diva-eng/BOKAKA/hardware/bokaka/connectors.kicad_sch

## KiCad design hardware/bokaka/connectors.kicad_sch (2026-01-29, an earlier design)

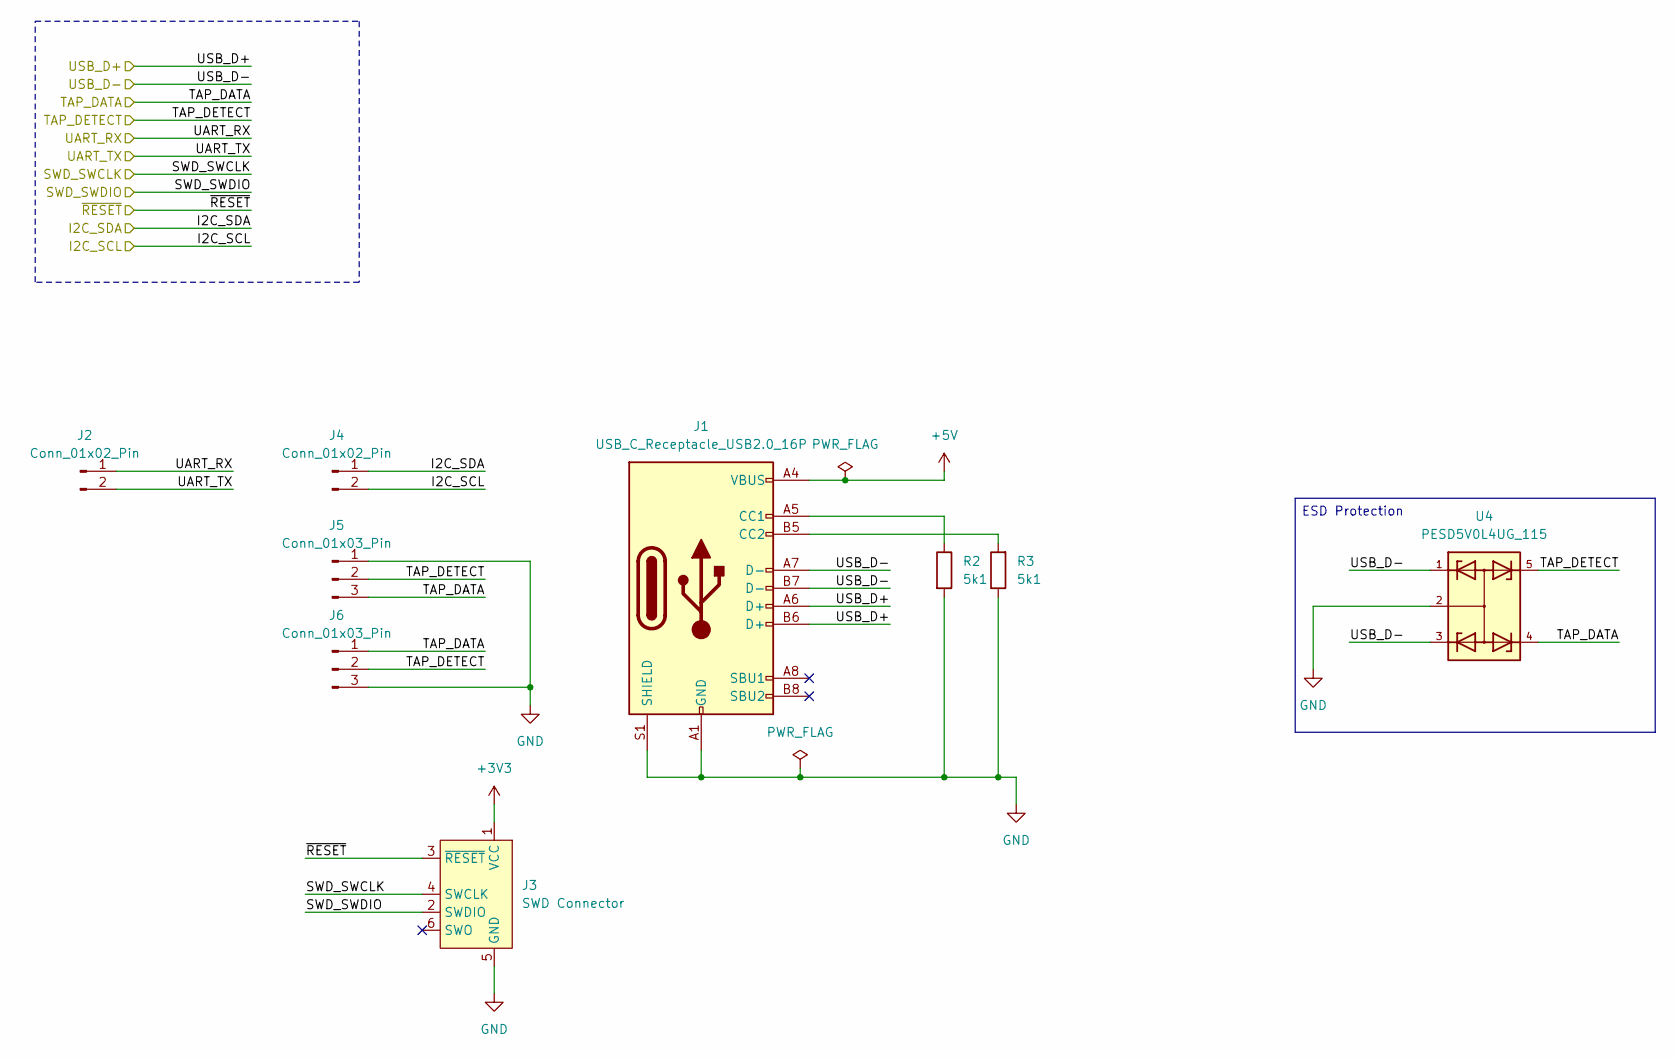
[picture p14: schematic connectors.kicad_sch]

Parts:
J1: USB_C_Receptacle_USB2.0_16P
J2, J4: Conn_01x02_Pin
J3: SWD Connector; Edge_Connect_6
J5, J6: Conn_01x03_Pin
R2, R3: 5k1; R_0402_1005Metric
U4: PESD5V0L4UG_115; SOT65P210X110-5N; PARTREV 04

Connections:
+3V3: J3.1 (VCC)
+5V: J1.A4 (VBUS), J1.A9 (VBUS), J1.B4 (VBUS), J1.B9 (VBUS)
GND: J1.A1 (GND), J1.A12 (GND), J1.B1 (GND), J1.B12 (GND), J1.S1 (SHIELD), J3.5 (GND), J5.1, J6.3, R2.2, R3.1, U4.2
I2C_SCL: J4.2
I2C_SDA: J4.1
unnamed: J1.A5 (CC1), R2.1
unnamed: J1.B5 (CC2), R3.2
SWD_SWCLK: J3.4 (SWCLK)
SWD_SWDIO: J3.2 (SWDIO)
TAP_DATA: J5.3, J6.1, U4.4
TAP_DETECT: J5.2, J6.2, U4.5
UART_RX: J2.1
UART_TX: J2.2
USB_D+: J1.A6 (D+), J1.B6 (D+)
USB_D-: J1.A7 (D-), J1.B7 (D-), U4.1, U4.3
~RESET: J3.3 (~RESET)

Notes on the sheet:
ESD Protection
