diva-eng/BOKAKA/hardware/bokaka/microcontroller.kicad_sch

## KiCad design hardware/bokaka/microcontroller.kicad_sch (2026-01-29, an earlier design)

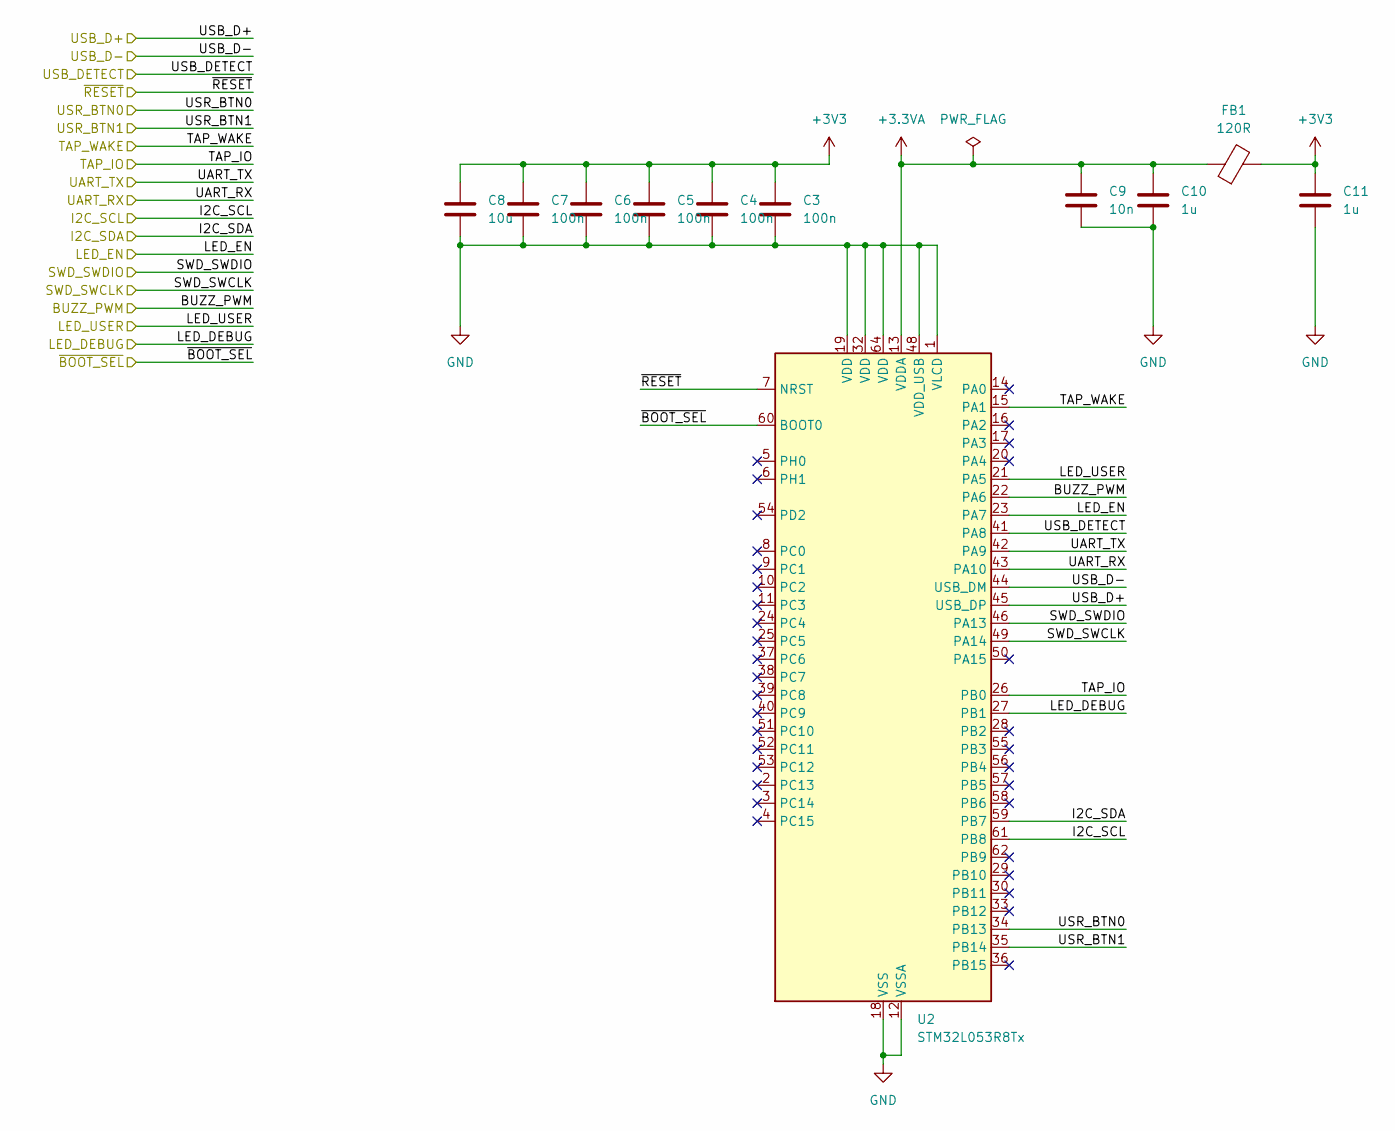
[picture p15: schematic microcontroller.kicad_sch]

Parts:
C3, C4, C5, C6, C7: 100n; C_0402_1005Metric
C8: 10u; C_0402_1005Metric
C9: 10n; C_0402_1005Metric
C10, C11: 1u; C_0402_1005Metric
FB1: 120R
U2: STM32L053R8Tx; LQFP-64_10x10mm_P0.5mm

Connections:
+3.3VA: C9.1, C10.1, FB1.1, U2.13 (VDDA)
+3V3: C3.1, C4.1, C5.1, C6.1, C7.1, C8.1, C11.1, FB1.2
BUZZ_PWM: U2.22 (PA6)
GND: C3.2, C4.2, C5.2, C6.2, C7.2, C8.2, C9.2, C10.2, C11.2, U2.1 (VLCD), U2.12 (VSSA), U2.18 (VSS), U2.19 (VDD), U2.31 (VSS), U2.32 (VDD), U2.47 (VSS), U2.48 (VDD_USB), U2.63 (VSS), U2.64 (VDD)
I2C_SCL: U2.61 (PB8)
I2C_SDA: U2.59 (PB7)
LED_DEBUG: U2.27 (PB1)
LED_EN: U2.23 (PA7)
LED_USER: U2.21 (PA5)
SWD_SWCLK: U2.49 (PA14)
SWD_SWDIO: U2.46 (PA13)
TAP_IO: U2.26 (PB0)
TAP_WAKE: U2.15 (PA1)
UART_RX: U2.43 (PA10)
UART_TX: U2.42 (PA9)
USB_D+: U2.45 (PA12)
USB_D-: U2.44 (PA11)
USB_DETECT: U2.41 (PA8)
USR_BTN0: U2.34 (PB13)
USR_BTN1: U2.35 (PB14)
~BOOT_SEL: U2.60 (BOOT0)
~RESET: U2.7 (NRST)
