diva-eng/BOKAKA/hardware/bokaka/peripherals.kicad_sch

## KiCad design hardware/bokaka/peripherals.kicad_sch (2026-01-29, an earlier design)

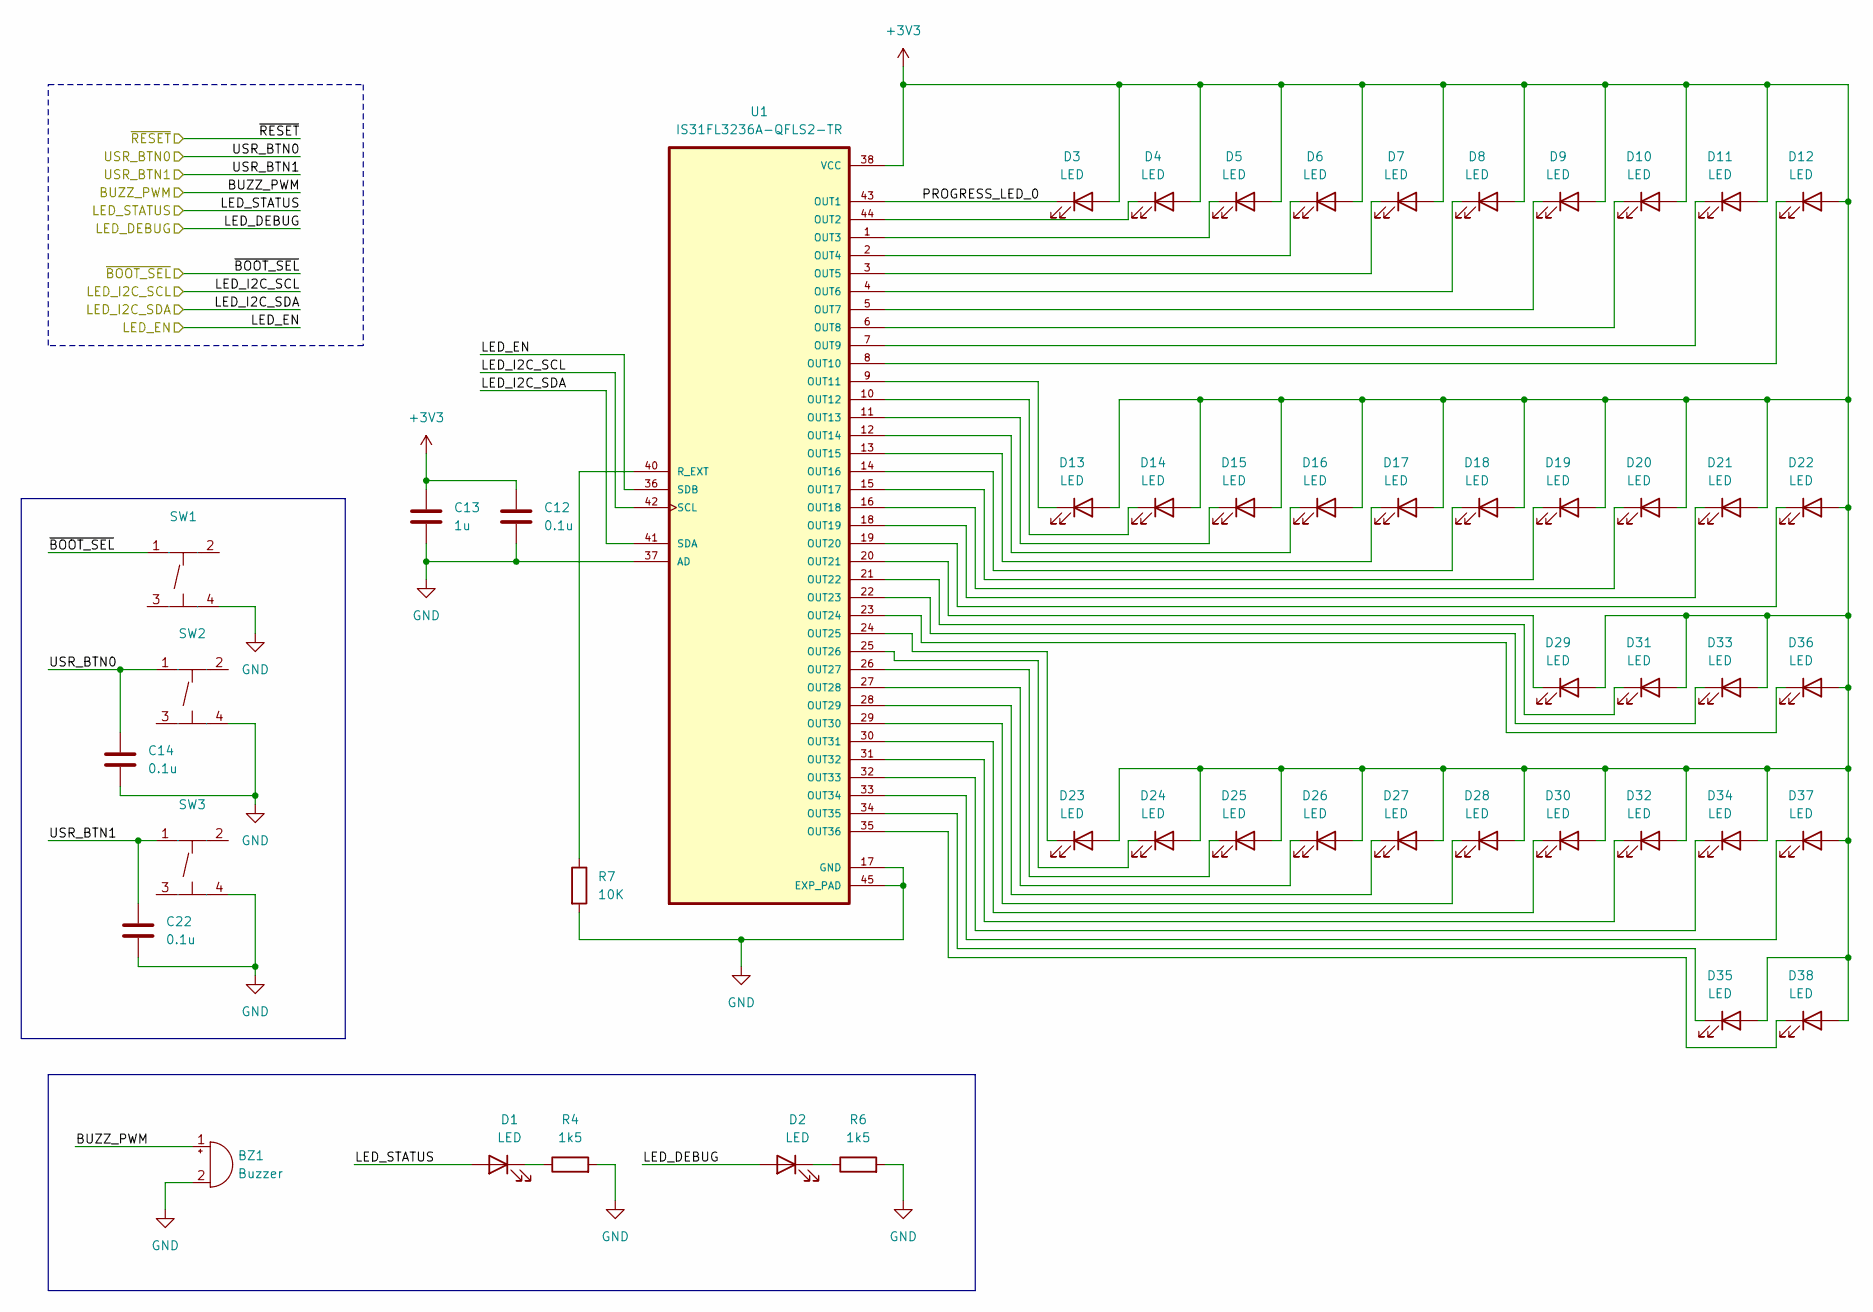
[picture p16: schematic peripherals.kicad_sch]

Parts:
BZ1: Buzzer; CUI_CPT-9019S-SMT
C12, C14, C22: 0.1u; C_0402_1005Metric
C13: 1u; C_0402_1005Metric
D1, D2, D3, D4, D5, D6, D7, D8, D9, D10, D11, D12, D13, D14, D15, D16, D17, D18, D19, D20, D21, D22, D23, D24, D25, D26, D27, D28, D29, D30, D31, D32, D33, D34, D35, D36, D37, D38: LED
R4, R6: 1k5; R_0402_1005Metric
R7: 10K; R_0402_1005Metric
SW1, SW2, SW3: SW-SMD_4P-L5.1-W5.1-P3.70-LS6.5-TL_H1.5; Manufacturer Part TS-1187A-B-A-B; LCSC Part Name 5.1*5.1*1.5mm 立贴 轻触开关
U1: IS31FL3236A-QFLS2-TR; QFN40P500X500X80-45N

Connections:
+3V3: C12.1, C13.1, D3.2 (A), D4.2 (A), D5.2 (A), D6.2 (A), D7.2 (A), D8.2 (A), D9.2 (A), D10.2 (A), D11.2 (A), D12.2 (A), D13.2 (A), D14.2 (A), D15.2 (A), D16.2 (A), D17.2 (A), D18.2 (A), D19.2 (A), D20.2 (A), D21.2 (A), D22.2 (A), D23.2 (A), D24.2 (A), D25.2 (A), D26.2 (A), D27.2 (A), D28.2 (A), D29.2 (A), D30.2 (A), D31.2 (A), D32.2 (A), D33.2 (A), D34.2 (A), D35.2 (A), D36.2 (A), D37.2 (A), D38.2 (A), U1.38 (VCC)
BUZZ_PWM: BZ1.1 (+)
GND: BZ1.2 (-), C12.2, C13.2, C14.2, C22.2, R4.2, R6.2, R7.2, SW1.4 (D), SW2.4 (D), SW3.4 (D), U1.17 (GND), U1.37 (AD), U1.39 (GND), U1.45 (EXP_PAD)
LED_DEBUG: D2.2 (A)
LED_EN: U1.36 (SDB)
LED_I2C_SCL: U1.42 (SCL)
LED_I2C_SDA: U1.41 (SDA)
LED_STATUS: D1.2 (A)
unnamed: D1.1 (K), R4.1
unnamed: D2.1 (K), R6.1
unnamed: D4.1 (K), U1.44 (OUT2)
unnamed: D5.1 (K), U1.1 (OUT3)
unnamed: D6.1 (K), U1.2 (OUT4)
unnamed: D7.1 (K), U1.3 (OUT5)
unnamed: D8.1 (K), U1.4 (OUT6)
unnamed: D9.1 (K), U1.5 (OUT7)
unnamed: D10.1 (K), U1.6 (OUT8)
unnamed: D11.1 (K), U1.7 (OUT9)
unnamed: D12.1 (K), U1.8 (OUT10)
unnamed: D13.1 (K), U1.9 (OUT11)
unnamed: D14.1 (K), U1.10 (OUT12)
unnamed: D15.1 (K), U1.11 (OUT13)
unnamed: D16.1 (K), U1.12 (OUT14)
unnamed: D17.1 (K), U1.13 (OUT15)
unnamed: D18.1 (K), U1.14 (OUT16)
unnamed: D19.1 (K), U1.15 (OUT17)
unnamed: D20.1 (K), U1.16 (OUT18)
unnamed: D21.1 (K), U1.18 (OUT19)
unnamed: D22.1 (K), U1.19 (OUT20)
unnamed: D23.1 (K), U1.24 (OUT25)
unnamed: D24.1 (K), U1.25 (OUT26)
unnamed: D25.1 (K), U1.26 (OUT27)
unnamed: D26.1 (K), U1.27 (OUT28)
unnamed: D27.1 (K), U1.28 (OUT29)
unnamed: D28.1 (K), U1.29 (OUT30)
unnamed: D29.1 (K), U1.20 (OUT21)
unnamed: D30.1 (K), U1.30 (OUT31)
unnamed: D31.1 (K), U1.21 (OUT22)
unnamed: D32.1 (K), U1.31 (OUT32)
unnamed: D33.1 (K), U1.22 (OUT23)
unnamed: D34.1 (K), U1.32 (OUT33)
unnamed: D35.1 (K), U1.34 (OUT35)
unnamed: D36.1 (K), U1.23 (OUT24)
unnamed: D37.1 (K), U1.33 (OUT34)
unnamed: D38.1 (K), U1.35 (OUT36)
unnamed: R7.1, U1.40 (R_EXT)
PROGRESS_LED_0: D3.1 (K), U1.43 (OUT1)
USR_BTN0: C14.1, SW2.1 (A)
USR_BTN1: C22.1, SW3.1 (A)
~BOOT_SEL: SW1.1 (A)
