diva-eng/BOKAKA/hardware/bokaka/power.kicad_sch

## KiCad design hardware/bokaka/power.kicad_sch (2026-01-29, an earlier design)

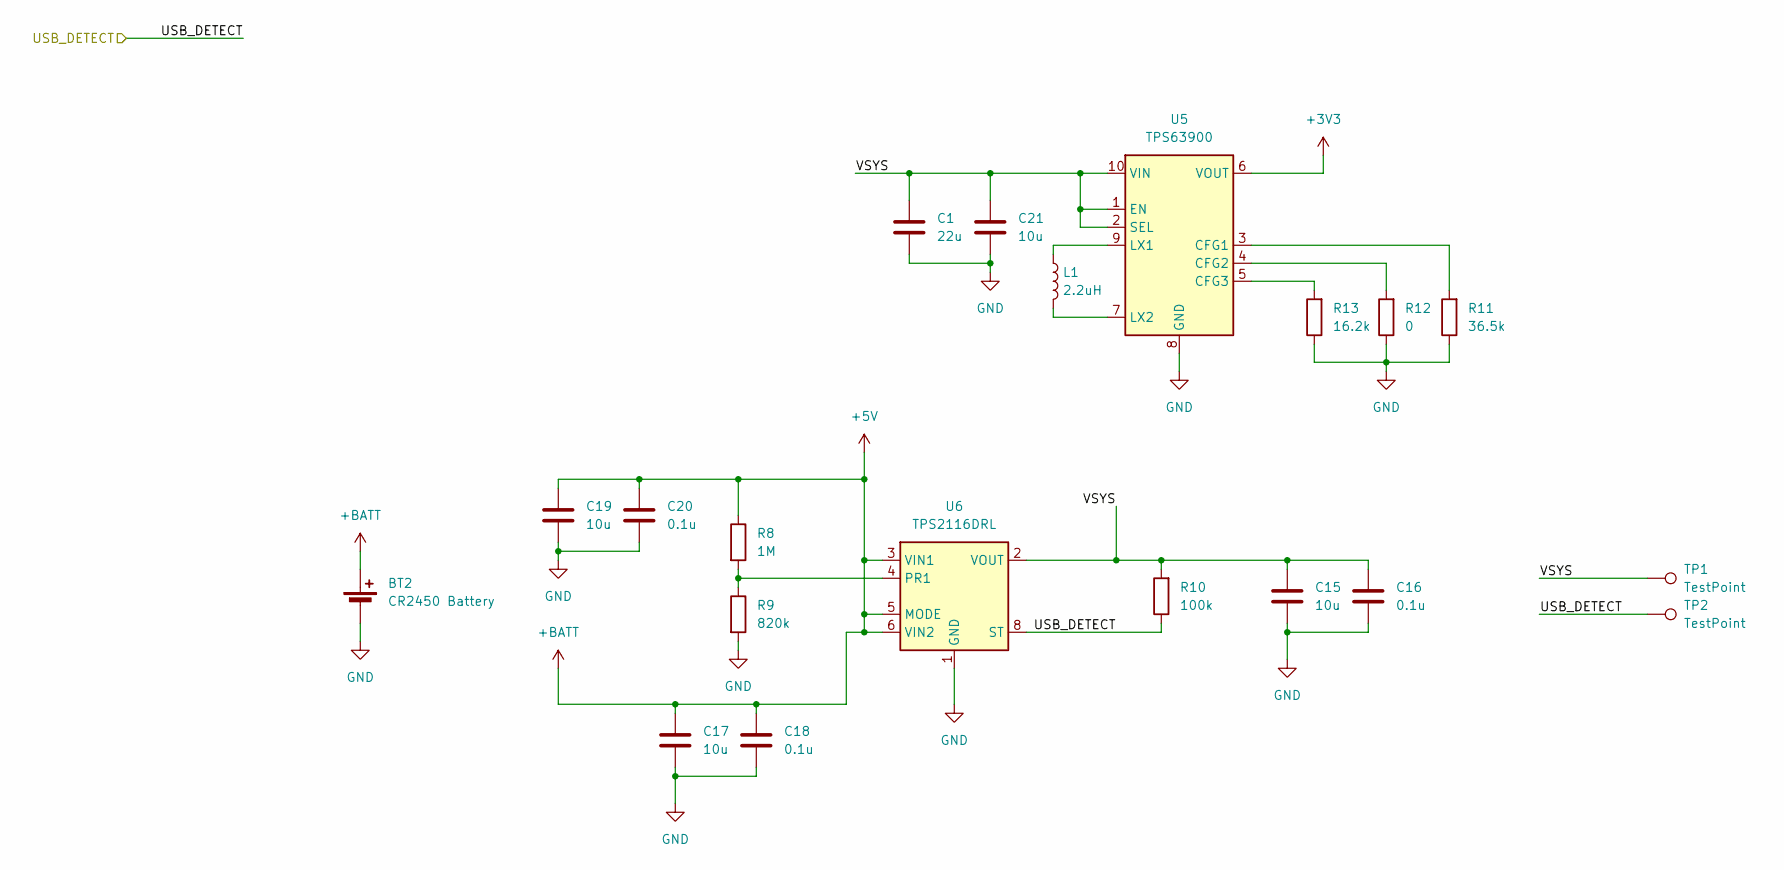
[picture p17: schematic power.kicad_sch]

Parts:
BT2: CR2450 Battery; BatteryHolder_Keystone_3009_1x2450
C1: 22u; C_0402_1005Metric
C15, C17, C19, C21: 10u; C_0402_1005Metric
C16, C18, C20: 0.1u; C_0402_1005Metric
L1: 2.2uH; L_0603_1608Metric
R8: 1M; R_0402_1005Metric
R9: 820k; R_0402_1005Metric
R10: 100k; R_0402_1005Metric
R11: 36.5k; R_0402_1005Metric
R12: 0; R_0402_1005Metric
R13: 16.2k; R_0402_1005Metric
TP1, TP2: TestPoint
U5: TPS63900; WSON-10-1EP_2.5x2.5mm_P0.5mm_EP1.2x2mm_ThermalVias
U6: TPS2116DRL; SOT-583-8

Connections:
+3V3: U5.6 (VOUT)
+5V: BT2.1 (+), C17.1, C18.1, C19.1, C20.1, R8.1, U6.3 (VIN1), U6.5 (MODE), U6.6 (VIN2)
GND: BT2.2 (-), C1.2, C15.2, C16.2, C17.2, C18.2, C19.2, C20.2, C21.2, R9.2, R11.1, R12.1, R13.1, U5.8 (GND), U5.11 (GND), U6.1 (GND)
unnamed: L1.1, U5.9 (LX1)
unnamed: L1.2, U5.7 (LX2)
unnamed: R8.2, R9.1, U6.4 (PR1)
unnamed: R11.2, U5.3 (CFG1)
unnamed: R12.2, U5.4 (CFG2)
unnamed: R13.2, U5.5 (CFG3)
USB_DETECT: R10.1, TP2.1, U6.8 (ST)
VSYS: C1.1, C15.1, C16.1, C21.1, R10.2, TP1.1, U5.1 (EN), U5.2 (SEL), U5.10 (VIN), U6.2 (VOUT), U6.7 (VOUT)
